dcknuth/pip_boy_replica/3d_models/speaker_holder.scad

// speaker holder
$fn = 50;

module speakerHolder(d, depth) {
  
}
