dcknuth/pip_boy_replica/3d_models/test_lipo_mount.scad

$fn = 100;
use <aaa_lipo_mount.scad>

lipoMount();
